robertengineerr/ereader/hardware/e_reader_v0.1/e_reader_v0.1.kicad_sch

## KiCad design hardware/e_reader_v0.1/e_reader_v0.1.kicad_sch (2026-03-10, an earlier design)

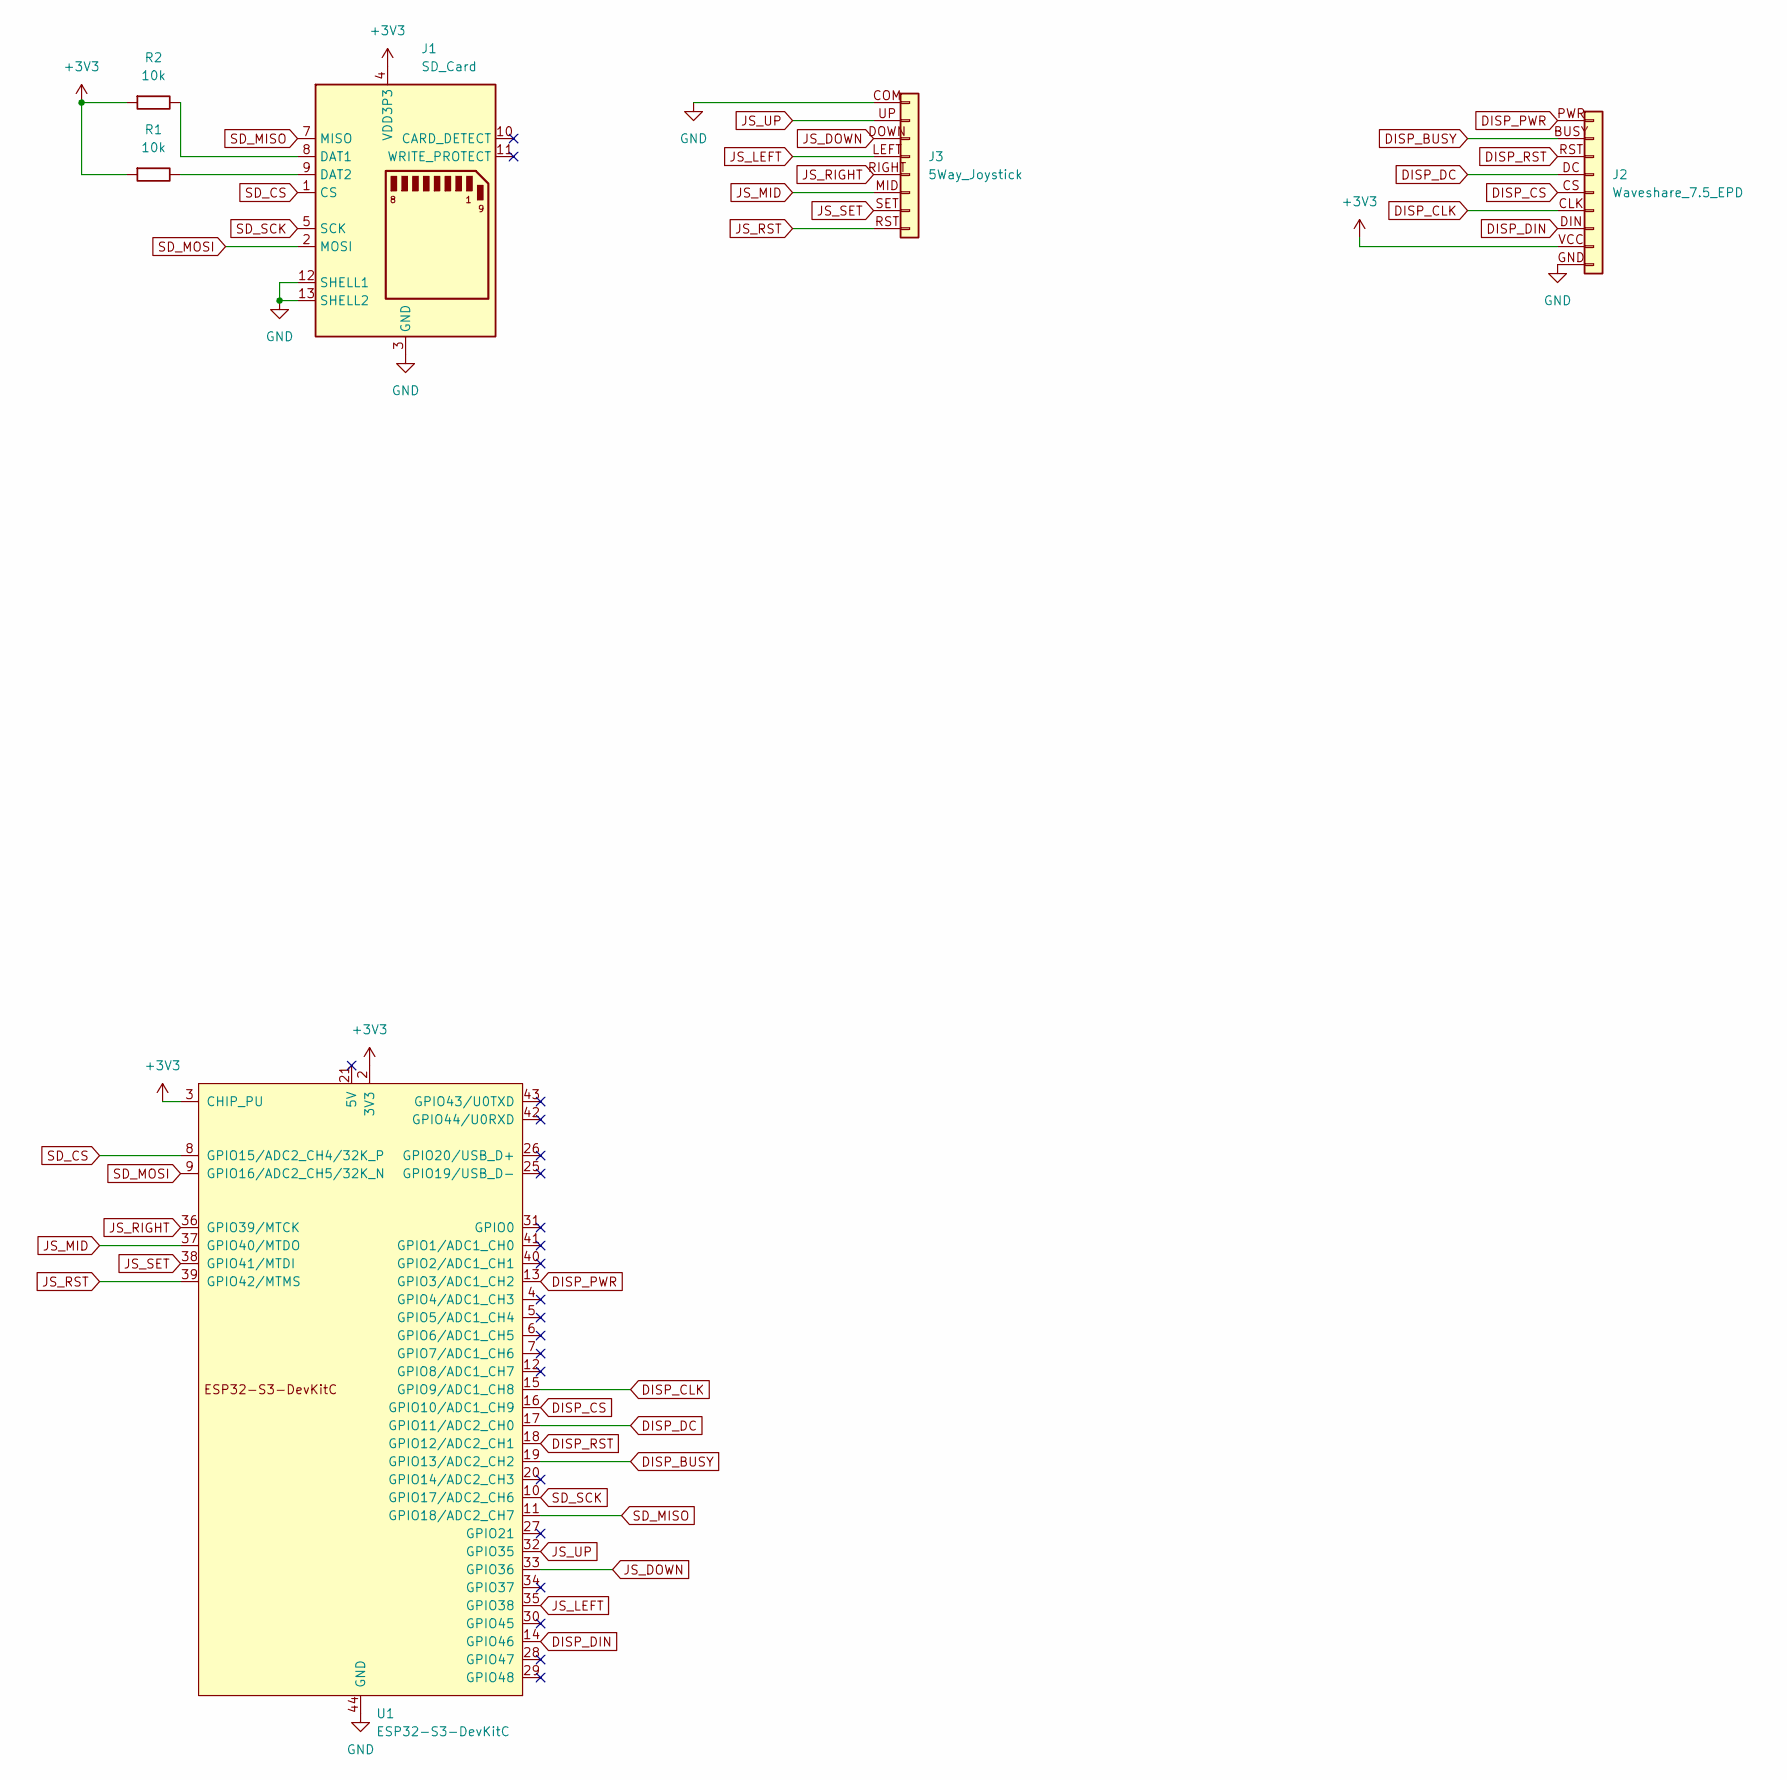
[picture p2: schematic e_reader_v0.1.kicad_sch]

Parts:
J1: SD_Card; SD_Kyocera_145638009211859+
J2: Waveshare_7.5_EPD
J3: 5Way_Joystick
R1, R2: 10k; R_Axial_DIN0207_L6.3mm_D2.5mm_P10.16mm_Horizontal
U1: ESP32-S3-DevKitC

Connections:
+3V3: J1.4 (VDD3P3), J2.VCC (Pin_7), R1.1, R2.1, U1.1 (3V3), U1.2 (3V3), U1.3 (CHIP_PU)
DISP_BUSY: J2.BUSY (Pin_2), U1.19 (GPIO13/ADC2_CH2)
DISP_CLK: J2.CLK (Pin_6), U1.15 (GPIO9/ADC1_CH8)
DISP_CS: J2.CS (Pin_5), U1.16 (GPIO10/ADC1_CH9)
DISP_DC: J2.DC (Pin_4), U1.17 (GPIO11/ADC2_CH0)
DISP_DIN: J2.DIN (Pin_6), U1.14 (GPIO46)
DISP_PWR: J2.PWR (Pin_1), U1.13 (GPIO3/ADC1_CH2)
DISP_RST: J2.RST (Pin_3), U1.18 (GPIO12/ADC2_CH1)
GND: J1.3 (GND), J1.6 (VSS), J1.12 (SHELL1), J1.13 (SHELL2), J2.GND (Pin_8), J3.COM (Pin_1), U1.22 (GND), U1.23 (GND), U1.24 (GND), U1.44 (GND)
JS_DOWN: J3.DOWN (Pin_3), U1.33 (GPIO36)
JS_LEFT: J3.LEFT (Pin_4), U1.35 (GPIO38)
JS_MID: J3.MID (Pin_6), U1.37 (GPIO40/MTDO)
JS_RIGHT: J3.RIGHT (Pin_5), U1.36 (GPIO39/MTCK)
JS_RST: J3.RST (Pin_8), U1.39 (GPIO42/MTMS)
JS_SET: J3.SET (Pin_7), U1.38 (GPIO41/MTDI)
JS_UP: J3.UP (Pin_2), U1.32 (GPIO35)
unnamed: J1.8 (DAT1), R2.2
unnamed: J1.9 (DAT2), R1.2
SD_CS: J1.1 (CS), U1.8 (GPIO15/ADC2_CH4/32K_P)
SD_MISO: J1.7 (MISO), U1.11 (GPIO18/ADC2_CH7)
SD_MOSI: J1.2 (MOSI), U1.9 (GPIO16/ADC2_CH5/32K_N)
SD_SCK: J1.5 (SCK), U1.10 (GPIO17/ADC2_CH6)
