robertengineerr/ereader/hardware/reference_material/Adafruit ESP32-S3 8MB No PSRAM.kicad_sch

## KiCad design hardware/reference_material/Adafruit ESP32-S3 8MB No PSRAM.kicad_sch (2026-03-09)

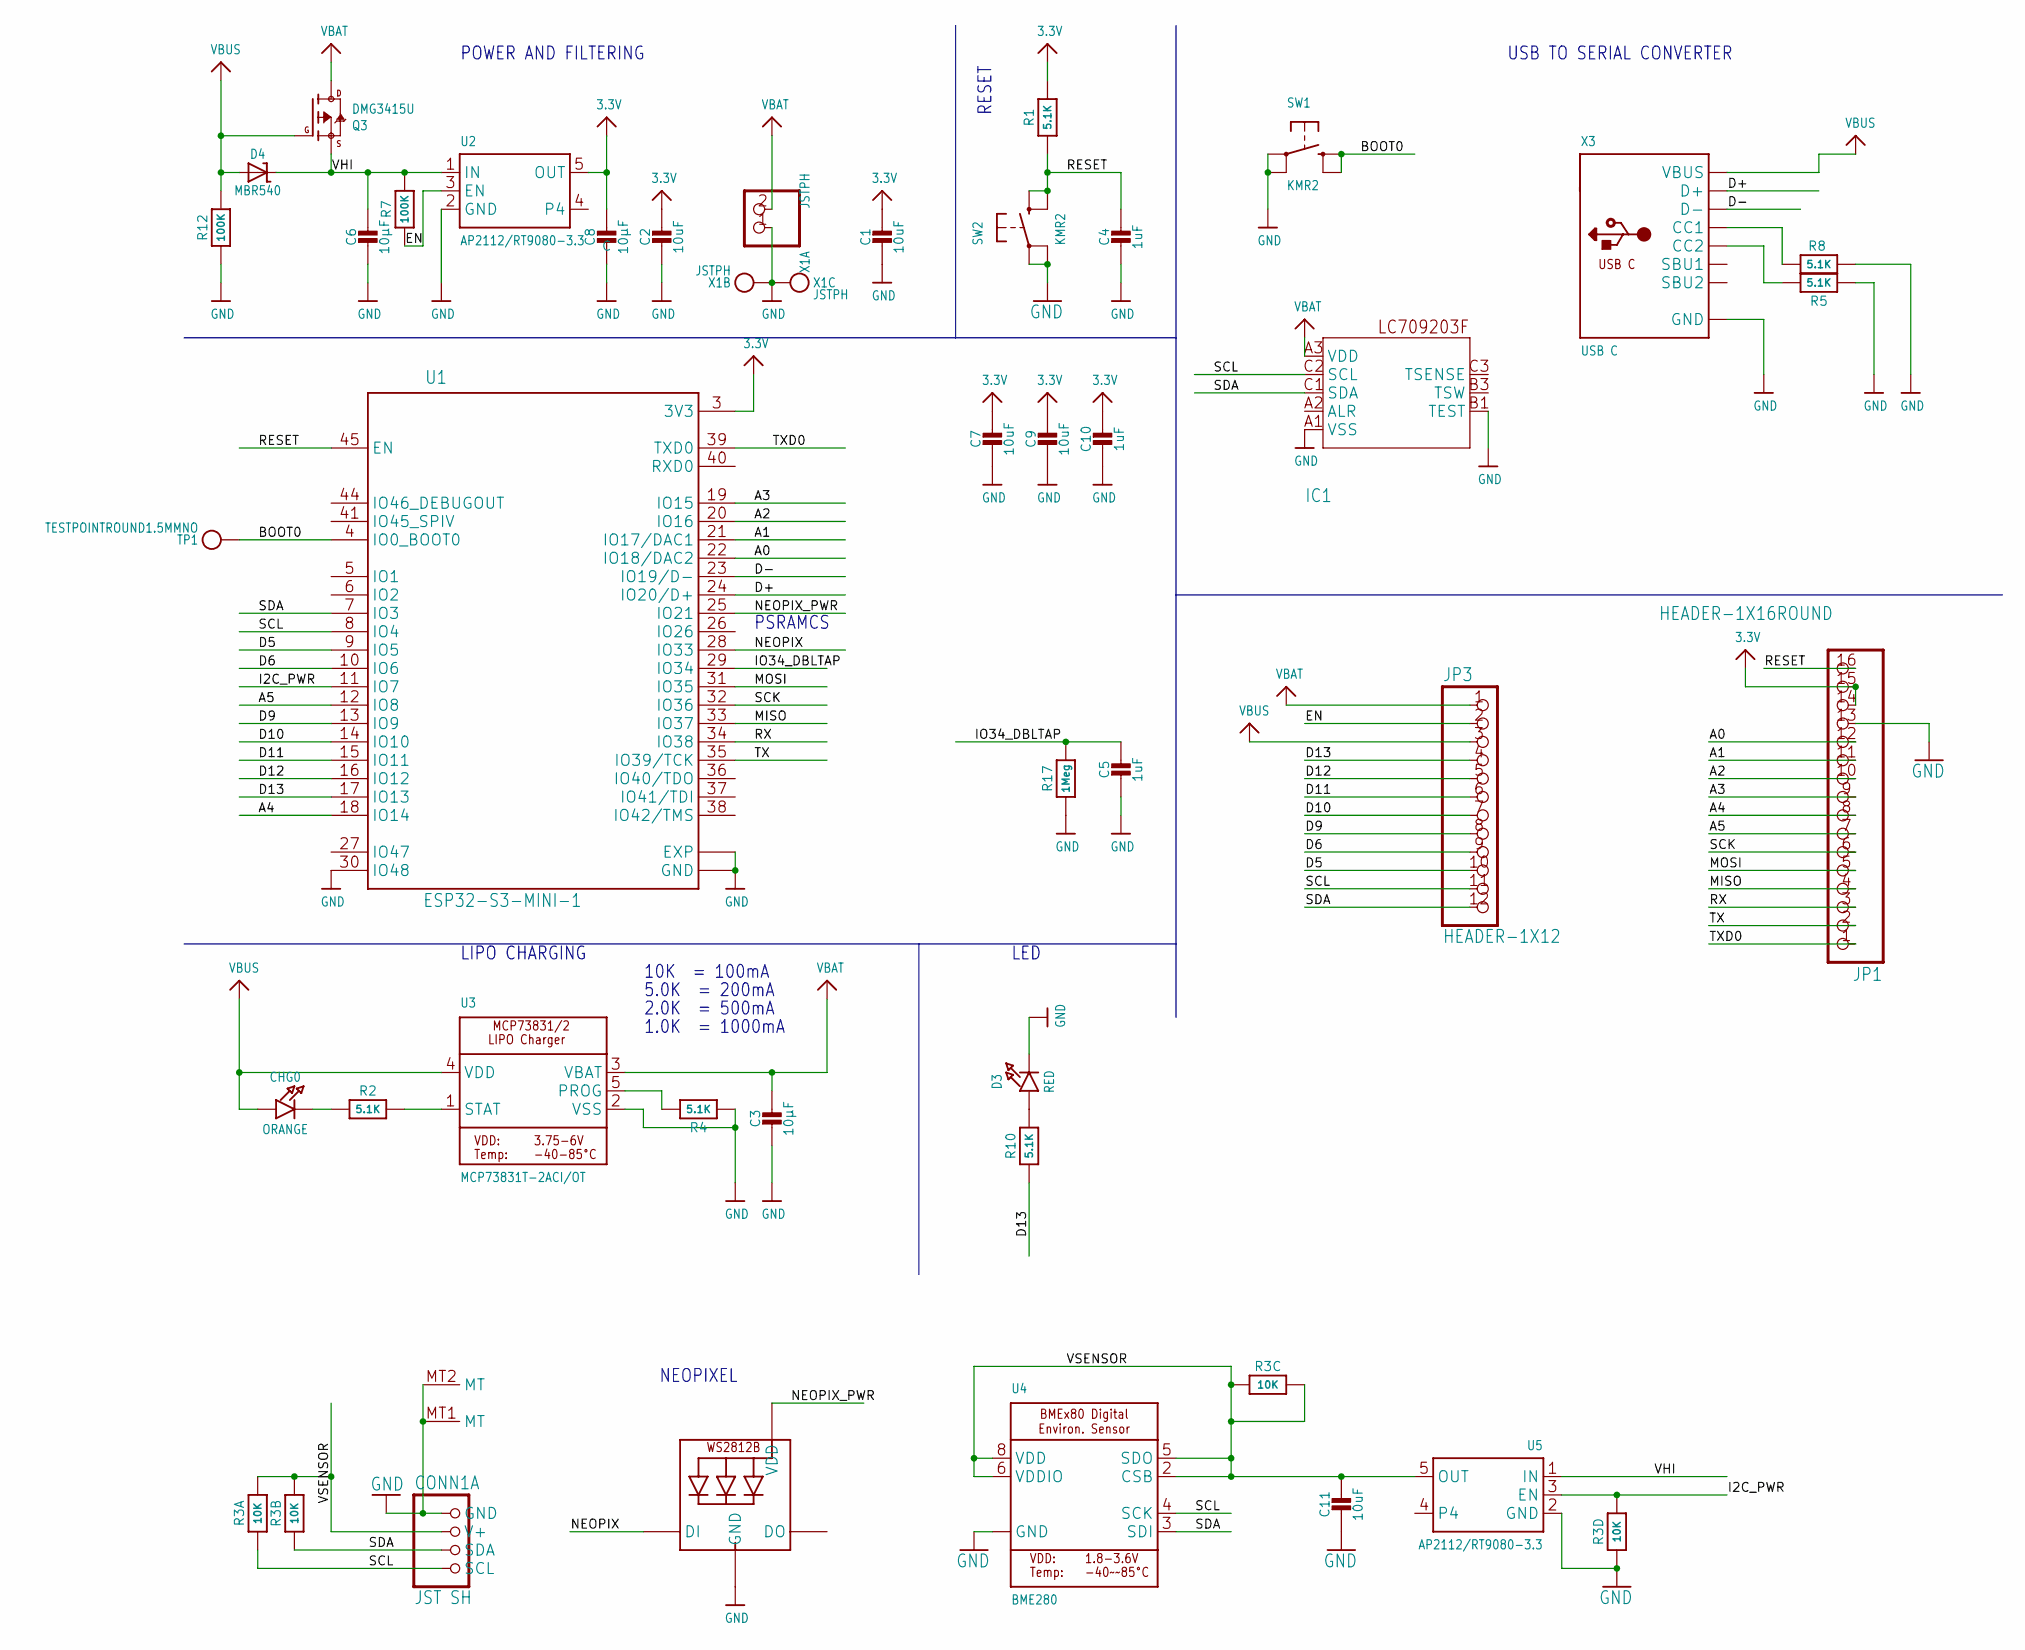
[picture p3: schematic Adafruit ESP32-S3 8MB No PSRAM.kicad_sch]

Parts:
C1, C2, C7, C9: 10uF; 0805-NO
C3, C6, C8: 10µF; 0805-NO
C4, C5, C10: 1uF; 0603-NO
C11: 10uF; _0805MP
CHG0: ORANGE; CHIPLED_0603_NOOUTLINE
CONN1: JST SH; JST_SH4_RA
D3: RED; CHIPLED_0603_NOOUTLINE
D4: MBR540; SOD-123
IC1: LC709203F/MH; WLCSP9
JP1: HEADER-1X16ROUND; 1X16_ROUND
JP3: HEADER-1X12; 1X12_ROUND
LED1: WS2812B_SK6805_1515; SK6805_1515
Q3: DMG3415U; SOT23-R
R1, R2, R4, R5, R8, R10: 5.1K; 0603-NO
R3: 10K; RESPACK_4X0603
R7, R12: 100K; 0603-NO
R17: 1Meg; 0603-NO
SW1, SW2: KMR2; BTN_KMR2_4.6X2.8
TP1: TESTPOINTROUND1.5MMNO; TESTPOINT_ROUND_1.5MM_NO
U1: ESP32-S3-MINI-1; QFN60_ESP32-S2-MINI-1_EXP
U2, U5: AP2112/RT9080-3.3; SOT23-5
U3: MCP73831T-2ACI/OT; SOT23-5
U4: BME280
X1: JSTPH; JSTPH2_BATT
X3: USB C; USB_C_CUSB31-CFM2AX-01-X

Connections:
3.3V: C1.1, C2.1, C7.1, C8.1, C9.1, C10.1, JP1.14, JP1.15, R1.2, U1.3 (3V3), U2.5 (OUT)
A0: JP1.12, U1.22 (IO18/DAC2)
A1: JP1.11, U1.21 (IO17/DAC1)
A2: JP1.10, U1.20 (IO16)
A3: JP1.9, U1.19 (IO15)
A4: JP1.8, U1.18 (IO14)
A5: JP1.7, U1.12 (IO8)
BOOT0: SW1.B (S), SW1.B' (S1), TP1.P$1, U1.4 (IO0_BOOT0)
D5: JP3.10, U1.9 (IO5)
D6: JP3.9, U1.10 (IO6)
D9: JP3.8, U1.13 (IO9)
D10: JP3.7, U1.14 (IO10)
D11: JP3.6, U1.15 (IO11)
D12: JP3.5, U1.16 (IO12)
D13: JP3.4, R10.1, U1.17 (IO13)
D+: U1.24 (IO20/D+), X3.A6 (D+), X3.B6 (D+)
D-: U1.23 (IO19/D-), X3.A7 (D-), X3.B7 (D-)
EN: JP3.2, R7.1, U2.3 (EN)
GND: C1.2, C2.2, C3.2, C4.2, C5.2, C6.2, C7.2, C8.2, C9.2, C10.2, C11.2, CONN1.1 (GND), CONN1.MT1 (MT), CONN1.MT2 (MT), D3.C, IC1.A1 (VSS), IC1.B1 (TEST), JP1.13, LED1.4 (GND), R3.4 (1), R4.1, R5.1, R8.1, R12.1, R17.1, SW1.A, SW1.A' (P1), SW2.A, SW2.A' (P1), U1.1 (GND), U1.2 (GND), U1.30 (IO48), U1.42 (GND), U1.43 (GND), U1.46 (GND), U1.47 (GND), U1.48 (GND), U1.49 (GND), U1.50 (GND), U1.51 (GND), U1.52 (GND), U1.53 (GND), U1.54 (GND), U1.55 (GND), U1.56 (GND), U1.57 (GND), U1.58 (GND), U1.59 (GND), U1.60 (GND), U1.61 (EXP), U1.62 (GND), U1.63 (GND), U1.64 (GND), U1.65 (GND), U1.66 (EXP), U1.67 (EXP), U1.68 (EXP), U1.69 (EXP), U1.70 (EXP), U1.71 (EXP), U1.72 (EXP), U1.73 (EXP), U2.2 (GND), U3.2 (VSS), U4.1 (GND), U4.7 (GND), U5.2 (GND), X1.1, X1.NC1, X1.NC2, X3.A1B12 (GND), X3.B1A12 (GND)
I2C_PWR: R3.5 (2), U1.11 (IO7), U5.3 (EN)
IO34_DBLTAP: C5.1, R17.2, U1.29 (IO34)
MISO: JP1.4, U1.33 (IO37)
MOSI: JP1.5, U1.31 (IO35)
NEOPIX: LED1.1 (DI), U1.28 (IO33)
NEOPIX_PWR: LED1.2 (VDD), U1.25 (IO21)
unnamed: CHG0.C, R2.1
unnamed: D3.A, R10.2
unnamed: R2.2, U3.1 (STAT)
unnamed: R4.2, U3.5 (PROG)
unnamed: R5.2, X3.B5 (CC2)
unnamed: R8.2, X3.A5 (CC1)
RESET: C4.1, JP1.16, R1.1, SW2.B (S), SW2.B' (S1), U1.45 (EN)
RX: JP1.3, U1.34 (IO38)
SCK: JP1.6, U1.32 (IO36)
SCL: CONN1.4 (SCL), IC1.C2 (SCL), JP3.11, R3.1, U1.8 (IO4), U4.4 (SCK)
SDA: CONN1.3 (SDA), IC1.C1 (SDA), JP3.12, R3.2 (1), U1.7 (IO3), U4.3 (SDI)
TX: JP1.2, U1.35 (IO39/TCK)
TXD0: JP1.1, U1.39 (TXD0)
VBAT: C3.1, IC1.A3 (VDD), JP3.1, Q3.3 (D), U3.3 (VBAT), X1.2
VBUS: CHG0.A, D4.A, JP3.3, Q3.1 (G), R12.2, U3.4 (VDD), X3.A4B9 (VBUS), X3.B4A9 (VBUS)
VHI: C6.1, D4.C, Q3.2 (S), R7.2, U2.1 (IN), U5.1 (IN)
VSENSOR: C11.1, CONN1.2 (V+), R3.3 (1), R3.6 (2), R3.7 (2), R3.8 (2), U4.2 (CSB), U4.5 (SDO), U4.6 (VDDIO), U4.8 (VDD), U5.5 (OUT)

Notes on the sheet:
POWER AND FILTERING
USB TO SERIAL CONVERTER
1.0K = 1000mA
LED
LIPO CHARGING
2.0K = 500mA
NEOPIXEL
10K = 100mA
RESET
PSRAMCS
5.0K = 200mA
